Supermagnum/Europe-ergo/prototype-build/20230216_135945.jpg

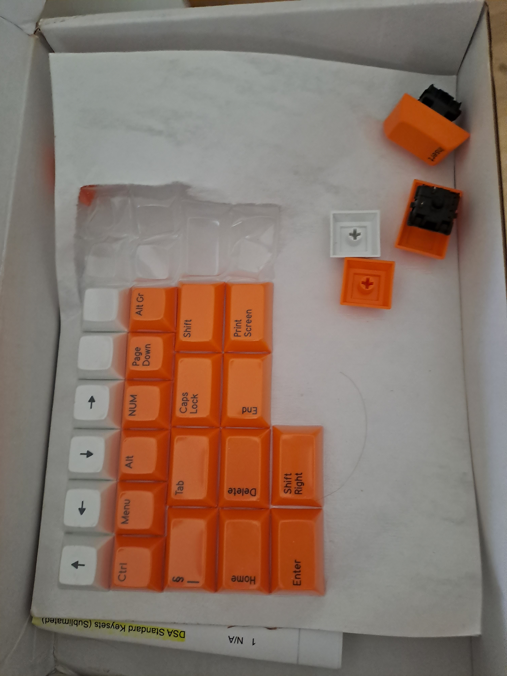
prototype-build/20230216_135945.jpg
