Supermagnum/Europe-ergo/prototype-build/20230313_192144.jpg

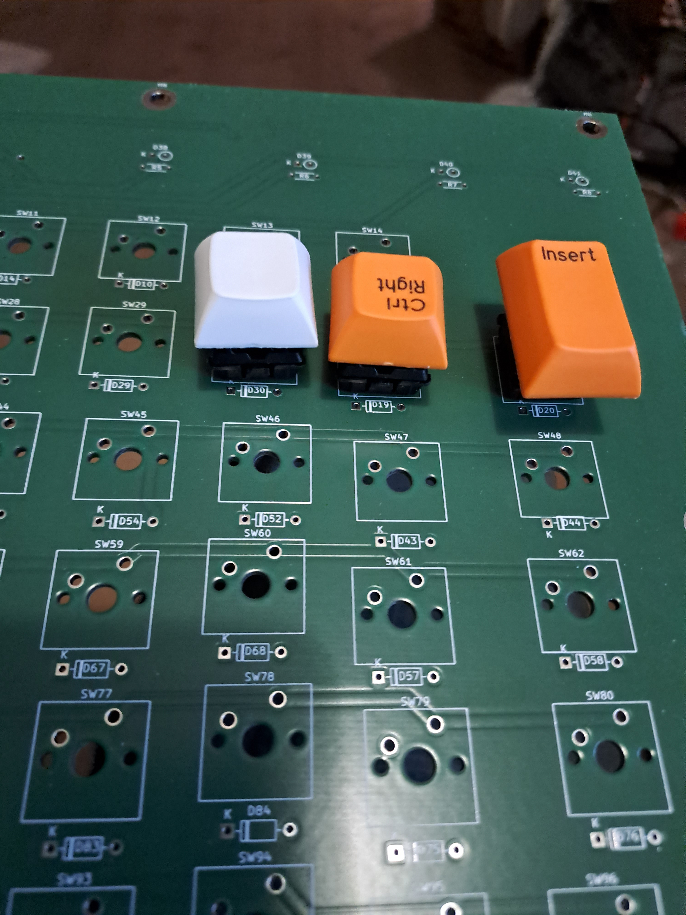
prototype-build/20230313_192144.jpg
