Supermagnum/Europe-ergo/prototype-build/20230413_181118.jpg

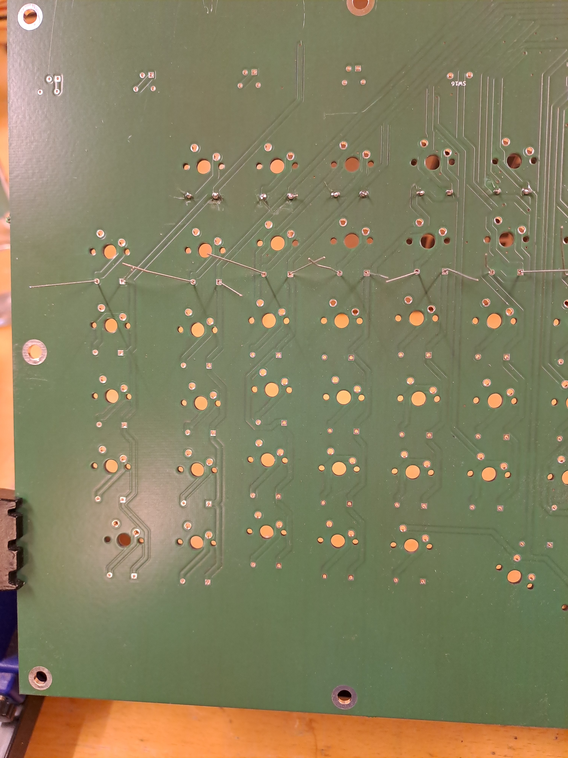
prototype-build/20230413_181118.jpg
