Supermagnum/Europe-ergo/prototype-build/20230518_172432.jpg

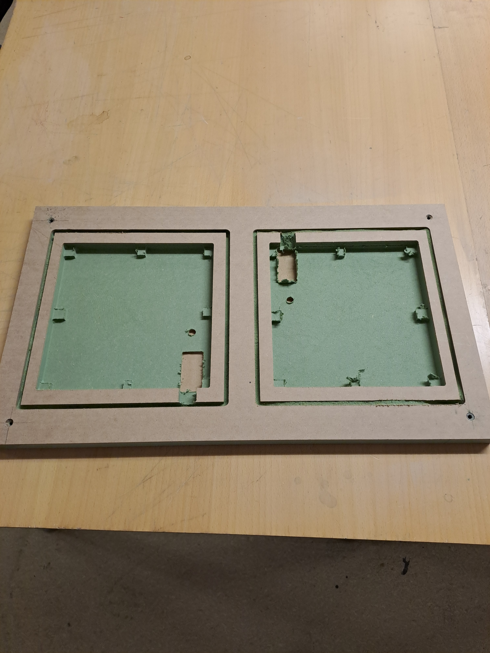
prototype-build/20230518_172432.jpg
