Supermagnum/Europe-ergo/prototype-build/20230619_185506.jpg

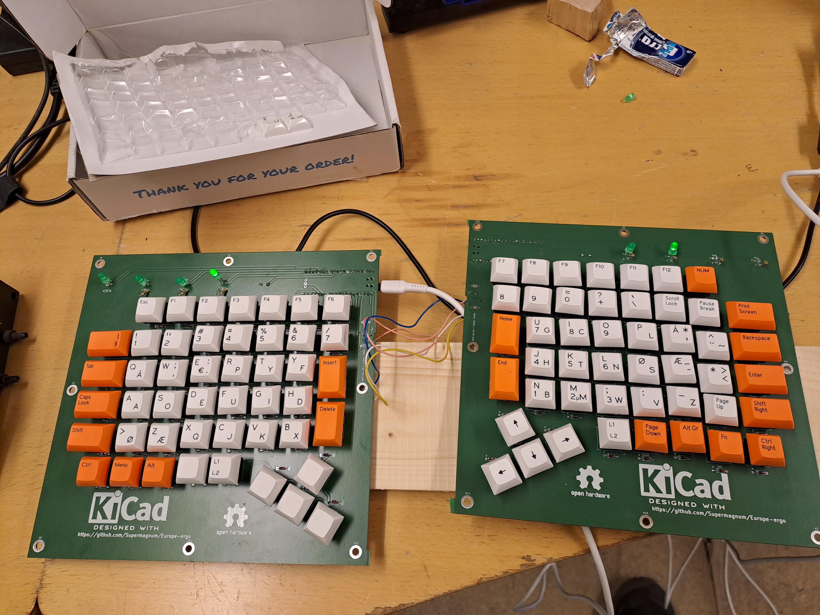
prototype-build/20230619_185506.jpg
