Supermagnum/Europe-ergo/prototype-build/20230810_175848.jpg

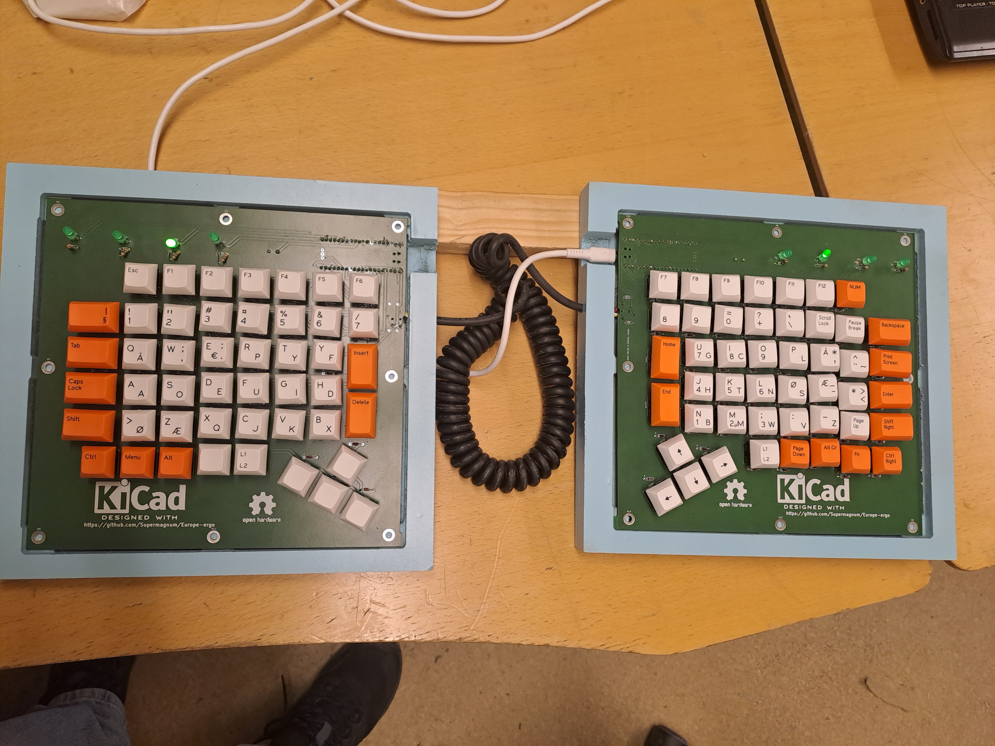
prototype-build/20230810_175848.jpg
