Supermagnum/Europe-ergo/prototype-build/prototype-firmware/proto-firmware-source/image.png

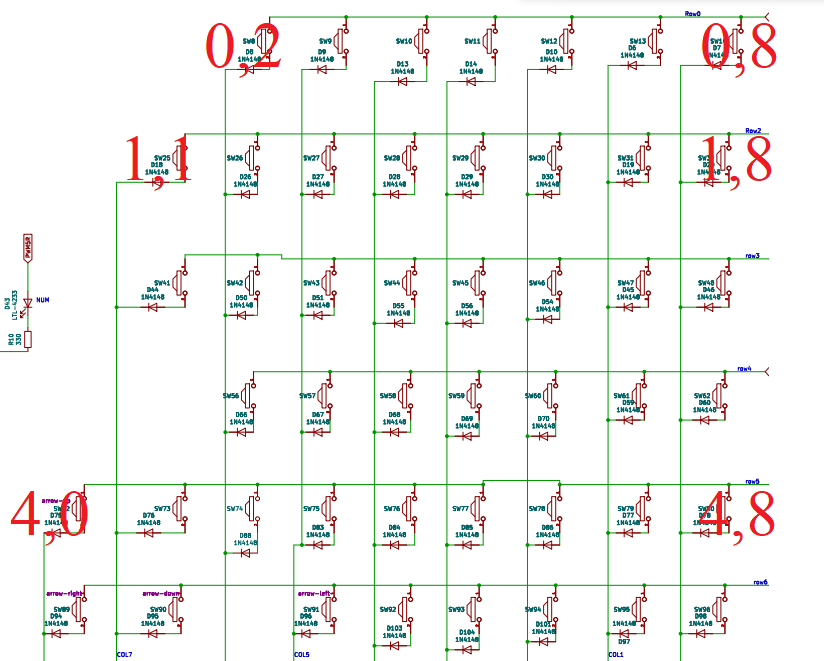
prototype-build/prototype-firmware/proto-firmware-source/image.png
