Supermagnum/Europe-ergo/prototype-build/20230330_183515.jpg

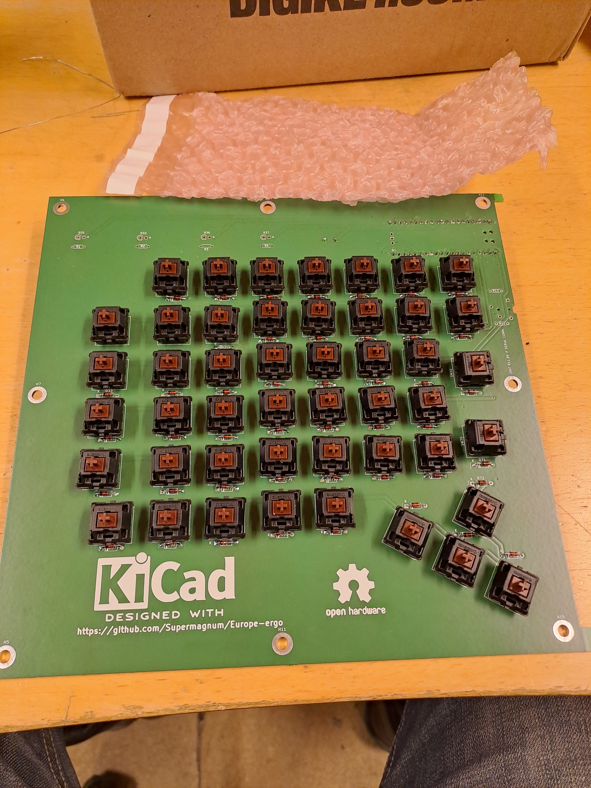
prototype-build/20230330_183515.jpg
